Odwalla-J/ODCON/PostLaunchFixes/SlideFix2.stl

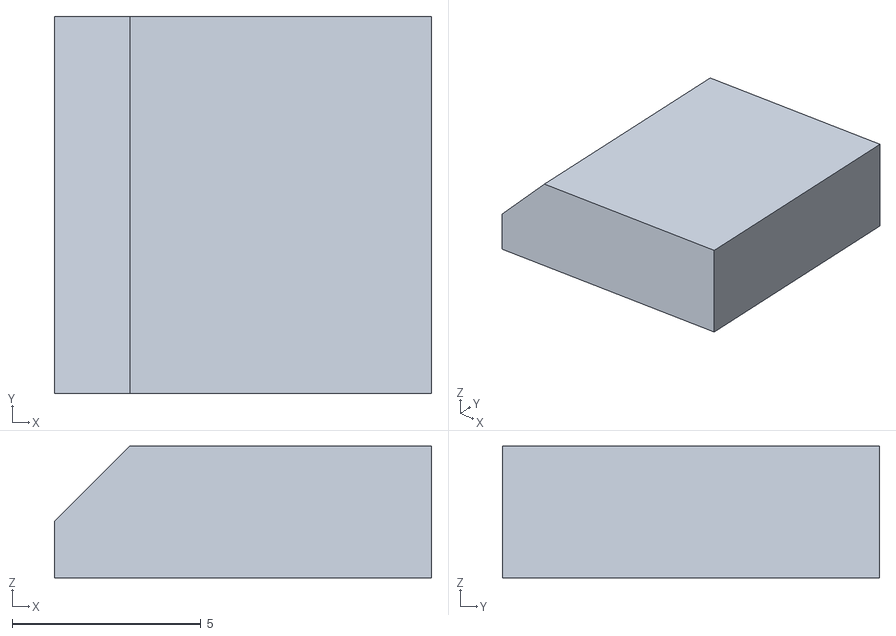
[picture p15: CAD file, 2022-05-01]
PostLaunchFixes/SlideFix2.stl
10.0 x 10.0 x 3.50
