Odwalla-J/ODCON/Frame/Barrel-WiiCam.stl

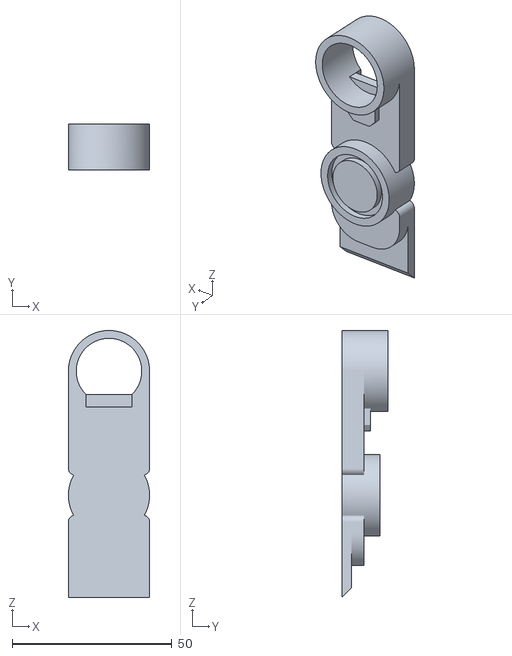
[picture p16: CAD file, 2022-04-30]
Frame/Barrel-WiiCam.stl
25.4 x 14.5 x 83.5
