Odwalla-J/ODCON/Misc/FrameAnchor.stl

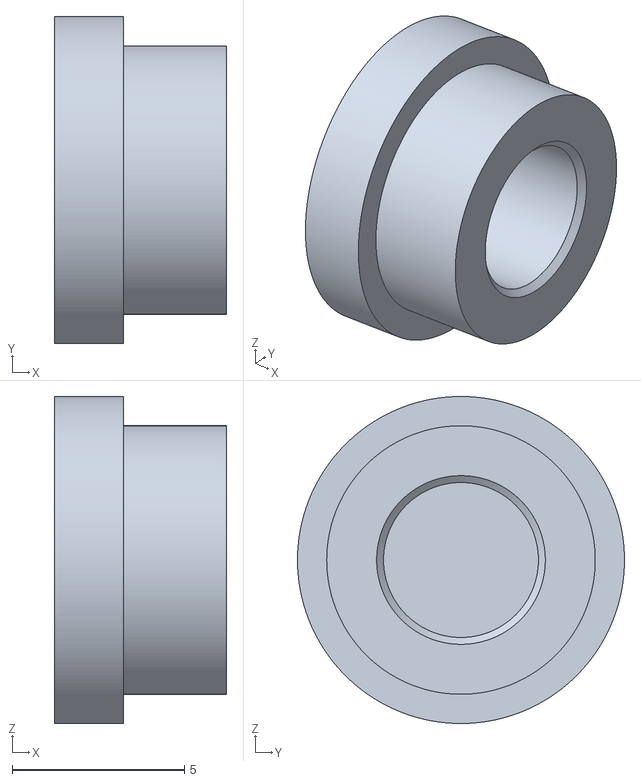
[picture p17: CAD file, 2022-04-30]
Misc/FrameAnchor.stl
5.00 x 9.50 x 9.50
