Odwalla-J/ODCON/PostLaunchFixes/SlideFix1.stl

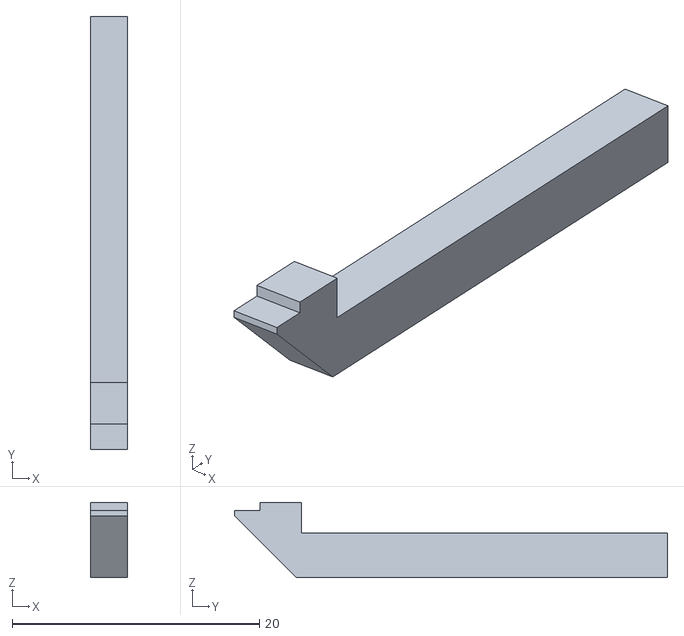
[picture p18: CAD file, 2022-05-01]
PostLaunchFixes/SlideFix1.stl
3.00 x 35.0 x 6.10
